freezweb/de.freezweb.heizungssteuerung/tmp/watermeter-roi-fix/alg_roi.jpg

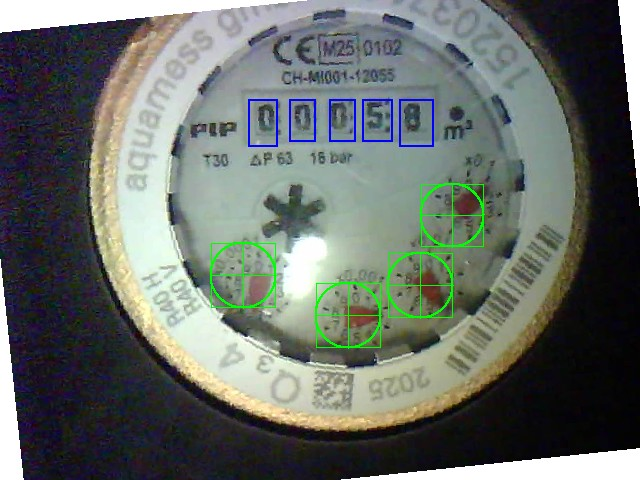
tmp/watermeter-roi-fix/alg_roi.jpg
