freezweb/de.freezweb.heizungssteuerung/tmp/watermeter-roi-fix/probe-_img_tmp_raw_jpg.jpg

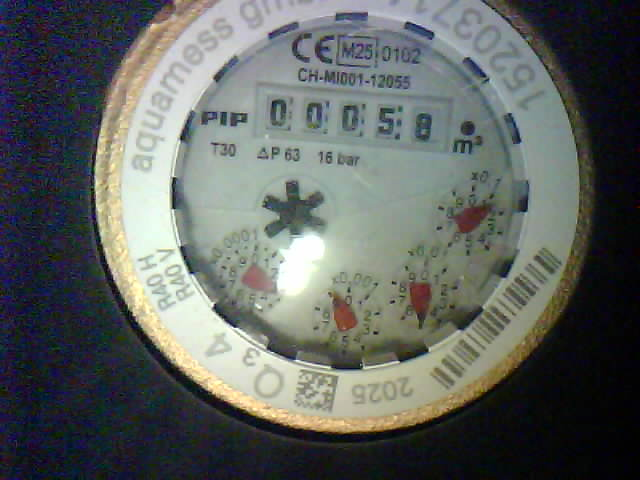
tmp/watermeter-roi-fix/probe-_img_tmp_raw_jpg.jpg
