freezweb/de.freezweb.heizungssteuerung/docs/通讯协议-0912(1)(1).docx

通讯协议Communication Protocol

Communication Protocol：9600bps，n，8,1，Communication time interval>200ms。

Support function codes :0x03,0x06，0x10
Register address | Readable | writable | Numerical range | Function Description | Remark
0(0x0000) | 0x03 | 0x06 0x10 | 0-1 | 0Power off 1Power on
1(0x0001) | 0x03 | 0x06 0x10 | 0-3 | 0 Automatic 1 Cooling 2 Heating 3 Ventilation
2(0x0002) | 0x03 | 0x06 0x10 | 0-4 | Set wind speed: 0 Auto wind 1 Low wind 2 Medium wind 3 High wind 4 Strong wind
3(0x0003) | 0x03 | 0x06 0x10 | 8-39 | Set temperature | Between the upper and lower limits
4(0x0004) | 0x03 | 0x06 0x10 | 0-1 | 0Up and down swing wind stop 1Up and down swing
5(0x0005) | 0x03 | 0x06 0x10 | 0-1 | 0Sway left and right, wind stops 1Swaying left and right
6(0x0006) | 0x03 | 0x06 0x10 | 0-1 | 0Electric heating off 1Electric heating is allowed to be turned on.
7(0x0007) | 0x03 | 0x06 0x10 | 0-1 | 0Screen display on 1Screen off
8(0x0008) | 0x03 | 0x06 0x10 | 0-1 | 0Child lock unlocking 1Child lock
9(0x0009) | 0x03 | 0x06 0x10 | 0-1 | 0Antifreeze function off 1Turn on antifreeze function
10(0x000A) | 0x03 | 0x06 0x10 | 20-39 | Anti-cold air setting temperature
11(0x000B) | 0x03 | 0x06 0x10 | 0-2 | 0Turn off the fan when the set temperature is reached. 1When the temperature reaches the set point, the fan does not turn off; when the temperature rises, the fan turns off. 2The fan does not turn off when cooling or heating reaches the set temperature.
12(0x000C) | 0x03 | 0x06 0x10 | 1-3 | Temperature control hysteresis
13(0x000D) | 0x03 | 0x06 0x10 | 0-1 | 0No power loss memory 1Has power failure memory
14(0x000E) | 0x03 | 0x06 0x10 | 1-99 | RS485 Address
20(0x0014) | 0x03 | | 0-84 | Ambient temperature | Actual temperature=n-9 0=-9 1=-8… 9=0 10=1 … 84=75
21(0x0015) | 0x03 | | 0-84 | Coil temperature | Actual temperature=N-9 0=-9 1=-8… 9=0 10=1 … 84=75
22(0x0016) | 0x03 | | 0-200 | Current real-time speed | rotational speed N*10 0Stop the wind 1-9Wind speed settings 1low wind 2medium-speed wind 3High-speed wind 4strong winds 10~200Wind speed value rotational speed N*10
23(0x0017) | 0x03 | | 0-65535 | Bit0:Ambient temperature sensor malfunction Bit1：Pipeline temperature sensor malfunction Bit2：Valve output markings Bit3：Passive point closure marker Bit4：Antifreeze in progress Bit5：Cold air protection in progress Bit6：Fan failure
