freezweb/de.freezweb.heizungssteuerung/hardware/pumpengruppe-rs485/tmp-ai-edge/live-2026-07-10-modeltest/downloads/log_data_data_1970-01-01.csv

1970-01-01T01:00:38+0100 | zaehlerstand | 33332.6666 | 58.01970 | 0.0000 | Rate too high - Read: 33332.6666 - Pre: 58.0197 - Rate: 33274.6469 | 2.8 | 2.8 | 2.8 | 2.8 | 2.8 | 7.0 | 7.0 | 7.0 | 7.0
1970-01-01T01:00:38+0100 | zaehlerstand | 11111.6666 | 58.01970 | 0.0000 | Rate too high - Read: 11111.6666 - Pre: 58.0197 - Rate: 11053.6469 | 1.0 | 1.0 | 1.0 | 1.0 | 1.0 | 7.0 | 7.0 | 7.0 | 7.0
