freezweb/de.freezweb.heizungssteuerung/hardware/pumpengruppe-rs485/tmp-ai-edge/live-2026-07-10-modeltest/downloads/log_data_data_2026-07-10.csv

2026-07-10T13:09:13+0200 | zaehlerstand | 33332.6666 | 33332.6666 | 33332.6666 | 0.0000 | no error | 2.8 | 2.8 | 2.8 | 2.8 | 2.8 | 7.0 | 7.0 | 7.0 | 7.0
2026-07-10T14:01:27+0200 | zaehlerstand | 00058.0197 | 58.0197 | 58.0197 | -33274.6469 | no error | 9.8 | 10.0 | 10.0 | 5.0 | 8.0 | 0.2 | 1.4 | 0.0 | 7.3
2026-07-10T14:17:40+0200 | zaehlerstand | 33332.6666 |  | 58.01970 | 0.0000 | Rate too high - Read: 33332.6666 - Pre: 58.0197 - Rate: 33274.6469 | 2.8 | 2.8 | 2.8 | 2.8 | 2.8 | 7.0 | 7.0 | 7.0 | 7.0
2026-07-10T14:40:03+0200 | zaehlerstand | 33332.6666 |  | 58.01970 | 0.0000 | Rate too high - Read: 33332.6666 - Pre: 58.0197 - Rate: 33274.6469 | 2.8 | 2.8 | 2.8 | 2.8 | 2.8 | 7.0 | 7.0 | 7.0 | 7.0
2026-07-10T14:45:20+0200 | zaehlerstand | 33332.6666 |  | 58.01970 | 0.0000 | Rate too high - Read: 33332.6666 - Pre: 58.0197 - Rate: 33274.6469 | 2.8 | 2.8 | 2.8 | 2.8 | 2.8 | 7.0 | 7.0 | 7.0 | 7.0
2026-07-10T15:41:46+0200 | zaehlerstand | 23344.4658 |  | 58.01970 | 0.0000 | Rate too high - Read: 23344.4658 - Pre: 58.0197 - Rate: 23286.4461 | 2.6 | 3.4 | 2.8 | 4.6 | 4.5 | 4.5 | 7.0 | 6.1 | 8.2
