freezweb/de.freezweb.heizungssteuerung/hardware/pumpengruppe-rs485/tmp-ai-edge/capture.jpg

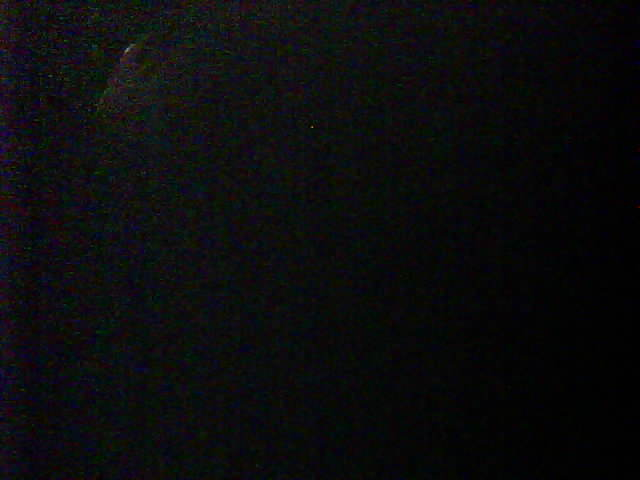
hardware/pumpengruppe-rs485/tmp-ai-edge/capture.jpg
