freezweb/de.freezweb.heizungssteuerung/hardware/pumpengruppe-rs485/tmp-ai-edge/live-2026-07-10-1545/reference.jpg

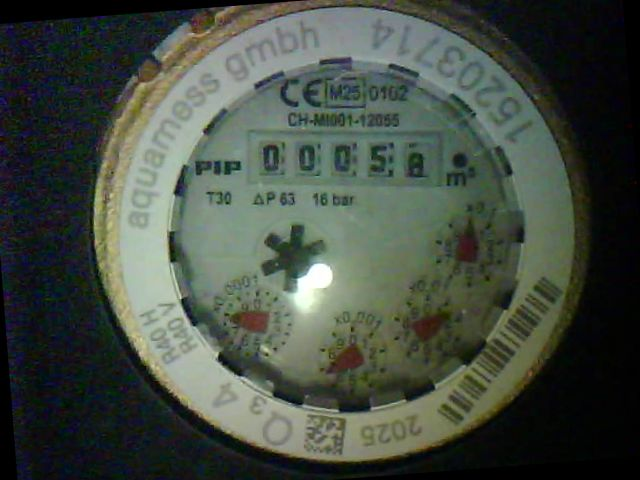
hardware/pumpengruppe-rs485/tmp-ai-edge/live-2026-07-10-1545/reference.jpg
