freezweb/de.freezweb.heizungssteuerung/hydraulik_waermepumpe_komponentenliste.xlsx

Sheet: Gesamtkonzept
Hydraulisches Gesamtkonzept Wärmepumpe / Heizung / Pool / Brunnenkühlung
Stand | 2026-06-25
Grundannahmen | 2× Monoblock-Wärmepumpe außen; je WP eigene Pumpe und motorisches Ventil/3WV, alternierend oder parallel fahrbar.
 | WP-Sammelschiene bei den Wärmepumpen; Sammelleitung über Dach/First in Heizungsraum; am First je VL/RL Entlüfter mit Absperrkugelhahn.
 | Heizungsraum wird komplett neu aufgebaut; vorhandenes Ausdehnungsgefäß bleibt. Dort sitzen Ölbrenner-Einbindung, Abgänge Pool und Nebengebäude sowie Weiterleitung ins Haupthaus.
 | Haupthausleitung bleibt bestehen; im Haupthaus bleiben die 2 bestehenden Heizkreise FBH und Radiatoren mit vorhandenen 3WV/Pumpen; Kaltwassergeräte/Fan-Coils bekommen neuen Kreis/HKV.
 | Brunnenpumpe bleibt; neu benötigt werden Brunnen-Wärmetauscher, Ventil(e), Gebäudekühlkreis-Armaturen und Mess-/Sicherheitskomponenten.
 | Pool bekommt Wärmetauscher und eigene Dosierstrecke mit pH, Redox/Chlor, pH-, Chlor und Flockungsmittel per Einzel-Schlauchpumpen; Steuerung erfolgt durch eigene Steuerung.
Schema WP-Seite | WP1 → Absperrung/Flex/Filter/Pumpe/Rückschlag/motorisches Ventil → WP-Sammelschiene
 | WP2 → Absperrung/Flex/Filter/Pumpe/Rückschlag/motorisches Ventil → WP-Sammelschiene
 | WP-Sammelschiene VL/RL → Sammelleitung über Dach/First → Heizungsraum
Schema Heizungsraum | Sammelleitung von WP-Seite → Haupt-Sammelpunkt warm VL/RL → Ölbrenner, Pool-WT, Nebengebäude, Haupthaus
Schema Haupthaus | Leitung aus Heizungsraum → Haupthaus-Verteiler → FBH-EG (bestehend), Radiatoren (bestehend), Kaltwassergeräte/Fan-Coils (neu)
Schema Brunnenkühlung | Brunnen offen: Brunnen → Brunnenpumpe → Filter/Ventil → Brunnen-WT → Ablauf/Schluckbrunnen
 | Gebäude geschlossen: Brunnen-WT → Kalt-VL → Fan-Coil-HKV → Kalt-RL → Brunnen-WT
Schema Pool | Heizungsseite: Hauptsammler → 3WV/Zonenventil → Pool-Heizkreispumpe → Pool-Plattenwärmetauscher → Rücklauf
 | Poolseite: Pool → Filterpumpe/Filter → Messstrecke/Dosierstellen → Pool-WT → zurück Pool
Betriebslogik WP | Nur WP1: Pumpe WP1 an, Ventil WP1 offen; WP2 aus und Ventil zu.
 | Nur WP2: Pumpe WP2 an, Ventil WP2 offen; WP1 aus und Ventil zu.
 | Parallel: beide Pumpen an, beide Ventile offen. Rückschlagventile verhindern Fehlzirkulation.
 | Abtauung/Störung: betroffene WP hydraulisch sperren, andere WP kann weiterlaufen.
Wichtige Hinweise | Komponentenliste ist eine Planungs-/Einkaufsliste, keine Ausführungsplanung nach DIN. Sicherheitsrelevante Auslegung, Druckverlust, MAG-Größe, Frostschutz und elektrische Verdrahtung vor Bau prüfen.
 | Günstige Links sind Einkaufs-/Suchlinks. Vor Bestellung: Anschlussmaß, Temperatur, Druck, Medium, Zulassung und Sauerstoffdichtheit prüfen.

Sheet: Komponentenliste
ID | Baugruppe | Einbauort / genaue Position | Komponente | Neu/Bestand | Menge | Dimension / Spezifikation | Funktion / Beschreibung | Günstiger Einkaufslink / Suchlink | Preis grob € | Gesamt grob € | Priorität | Hinweise / Prüfen
WP-001 | WP-Seite außen | WP1 direkt am 1" Außengewinde VL/RL | Kurzer flexibler Heizungsanschluss | Neu | 2 | 1" IG/AG, Edelstahlwellrohr/Panzerschlauch, 30–50 cm | Schwingungsentkopplung direkt an WP1, nicht als lange Leitung verwenden | https://www.amazon.de/s?k=edelstahlwellrohr+1+zoll+flexibel+heizung | 25 | 50 | hoch | Temperatur/Druck und Sauerstoffthema egal, da Metall; möglichst kurz halten
WP-002 | WP-Seite außen | WP2 direkt am 1" Außengewinde VL/RL | Kurzer flexibler Heizungsanschluss | Neu | 2 | 1" IG/AG, Edelstahlwellrohr/Panzerschlauch, 30–50 cm | Schwingungsentkopplung direkt an WP2 | https://www.amazon.de/s?k=edelstahlwellrohr+1+zoll+flexibel+heizung | 25 | 50 | hoch | Möglichst kurze flexible Strecke
WP-003 | WP-Seite außen | Je WP vor und nach Filter/Pumpe | Kugelhahn / Absperrhahn | Neu | 8 | 1" IG, voller Durchgang | Absperren von WP1/WP2 VL/RL für Wartung | https://www.amazon.de/s?k=kugelhahn+1+zoll+heizung | 12 | 96 | hoch | Messing/Heizung geeignet; full bore bevorzugt
WP-004 | WP-Seite außen | WP1 Rücklauf vor Wärmepumpe | Schmutzfänger Y-Filter | Neu | 1 | 1" IG, Heizung | Schützt WP1-Wärmetauscher/Pumpe vor Schmutz | https://www.amazon.de/s?k=schmutzf%C3%A4nger+1+zoll+heizung | 18 | 18 | hoch | Maschenweite nicht zu fein, Spülbarkeit sinnvoll
WP-005 | WP-Seite außen | WP2 Rücklauf vor Wärmepumpe | Schmutzfänger Y-Filter | Neu | 1 | 1" IG, Heizung | Schützt WP2-Wärmetauscher/Pumpe vor Schmutz | https://www.amazon.de/s?k=schmutzf%C3%A4nger+1+zoll+heizung | 18 | 18 | hoch | Herstellerforderung der WP prüfen
WP-006 | WP-Seite außen | WP1 Vorlauf/Rücklauf-Einbindung vor WP-Sammelschiene | WP1-Umwälzpumpe | Neu | 1 | mind. 25-80/180, besser nach Druckverlustrechnung; ca. 3,1 m³/h | Eigenständige Förderpumpe für WP1, weil WP laut Lastenheft keine integrierte Pumpe hat | https://chm-pumpen.de/Heizungspumpe-Auto-25-80-180/248 | 91 | 91 | hoch | Billigpumpe als Sparvariante; Premiumvergleich Grundfos 32-80 separat prüfen
WP-007 | WP-Seite außen | WP2 Vorlauf/Rücklauf-Einbindung vor WP-Sammelschiene | WP2-Umwälzpumpe | Neu | 1 | mind. 25-80/180, besser nach Druckverlustrechnung; ca. 3,1 m³/h | Eigenständige Förderpumpe für WP2 | https://chm-pumpen.de/Heizungspumpe-Auto-25-80-180/248 | 91 | 91 | hoch | Wenn 63er langer Strang und viele Bögen: ggf. 32-80 wählen
WP-008 | WP-Seite außen | Direkt hinter WP1-Pumpe Richtung Sammelschiene | Rückschlagventil | Neu | 1 | 1" oder passend zur Pumpenverschraubung | Verhindert Rückströmung durch stehende WP1 | https://www.amazon.de/s?k=r%C3%BCckschlagventil+1+zoll+heizung | 15 | 15 | hoch | Strömungsrichtung eindeutig markieren
WP-009 | WP-Seite außen | Direkt hinter WP2-Pumpe Richtung Sammelschiene | Rückschlagventil | Neu | 1 | 1" oder passend zur Pumpenverschraubung | Verhindert Rückströmung durch stehende WP2 | https://www.amazon.de/s?k=r%C3%BCckschlagventil+1+zoll+heizung | 15 | 15 | hoch | Federbelastet mit geringem Öffnungsdruck bevorzugt
WP-010 | WP-Seite außen | WP1 zwischen Pumpe/Rückschlag und WP-Sammelschiene | Motorisches Zonenventil oder 3WV WP1 | Neu | 1 | 1" bis 1¼", 230 V oder 24 V, Auf/Zu | WP1 hydraulisch in Sammelkreis ein-/auskoppeln für Alternation/Parallelbetrieb | https://www.idealo.de/preisvergleich/Liste/116030402/2-wege-motorkugelhahn-230v.html | 38 | 38 | hoch | 2WV reicht meist; echtes 3WV nur nötig, wenn Bypass/Umlenkung geplant
WP-011 | WP-Seite außen | WP2 zwischen Pumpe/Rückschlag und WP-Sammelschiene | Motorisches Zonenventil oder 3WV WP2 | Neu | 1 | 1" bis 1¼", 230 V oder 24 V, Auf/Zu | WP2 hydraulisch in Sammelkreis ein-/auskoppeln | https://www.idealo.de/preisvergleich/Liste/116030402/2-wege-motorkugelhahn-230v.html | 38 | 38 | hoch | Stellzeit/Fail-Position beachten
WP-012 | WP-Seite außen | WP1/WP2 bis WP-Sammelschiene | PP-RCT Heizungsrohr | Neu | 20 | 50 mm, sauerstoffdicht DIN 4726, Stabi/Alu/Faser | Kurze großdimensionierte Anbindung beider Wärmepumpen an WP-Sammelschiene | https://www.kwerk.de/rohrsysteme/pp-rct-rohrsysteme/pp-rct-rohre/rohre-mehrlagig/stabitec-ct/pp-rct-alu-druckrohr-stabitec-ct-20mpa-gruen/ | 8 | 160 | hoch | Nur heizungsgeeignet und sauerstoffdicht; Menge Meter grob
WP-013 | WP-Seite außen | Sammelleitung WP-Sammelschiene → Heizungsraum über First | PP-RCT Heizungsrohr Sparvariante | Neu | 50 | 63 mm, sauerstoffdicht DIN 4726, Stabi/Alu/Faser | Gemeinsamer VL/RL über Dach/First in Heizungsraum | https://www.kwerk.de/rohrsysteme/pp-rct-rohrsysteme/pp-rct-rohre/rohre-mehrlagig/stabitec-ct/pp-rct-alu-druckrohr-stabitec-ct-20mpa-gruen/ | 12 | 600 | hoch | 63 mm ist Material-/Werkzeug-Sparvariante; 75 mm hydraulisch besser
WP-014 | WP-Seite außen | Alternative zur 63er Sammelleitung | PP-RCT Heizungsrohr Komfortvariante | Optional | 50 | 75 mm, sauerstoffdicht DIN 4726 | Hydraulisch bessere gemeinsame Sammelleitung | https://www.rohrleitungssysteme.de/pp-r-rohrsysteme/index.php?zurueck=1 | 18 | 900 | mittel | Nur wenn Werkzeug/Fittings bezahlbar verfügbar
WP-015 | Werkzeug | Für PP-RCT 40/50/63 mm | Muffenschweißgerät | Neu | 1 | bis 63 mm, passende Muffen | Werkzeug zum Verarbeiten von PP-R/PP-RCT | https://www.amazon.de/s?k=muffenschwei%C3%9Fger%C3%A4t+63mm+ppr | 60 | 60 | hoch | Bei Alu-Stabi zusätzlich Schälgerät nötig; Probeschweißungen machen
WP-016 | Werkzeug | Für PP-RCT Alu-Stabi Rohr | Schälgerät / Rohrschäler | Neu | 1 | 40/50/63 mm passend zum Rohrsystem | Entfernt Aluschicht vor Schweißung bei Stabi-Rohr | https://www.rohrleitungssysteme.de/pp-r-rohrsysteme/index.php?zurueck=1 | 80 | 80 | hoch | Systemgebunden; beim Rohrhändler passend mitbestellen
WP-017 | WP-Sammelschiene außen | An Sammel-VL und Sammel-RL | Temperaturfühler Anlegefühler | Neu | 2 | PT1000, Anlegefühler | Messung WP-Sammel-VL/RL für Steuerung | https://www.amazon.de/s?k=pt1000+anlegef%C3%BChler+heizung | 15 | 30 | hoch | An Rohr gut wärmeleitend befestigen und dämmen
WP-018 | WP-Sammelschiene außen | Tiefpunkt WP-Sammelschiene VL/RL | KFE-Hahn / Entleerung | Neu | 2 | 1/2" oder 3/4" | Entleeren/Spülen der WP-Seite | https://www.amazon.de/s?k=kfe+hahn+1%2F2+heizung | 8 | 16 | mittel | Mit Schlauchanschluss
WP-019 | Dach/First | Höchster Punkt der Sammelleitung, Vorlauf | T-Stück + Kugelhahn + automatischer Entlüfter | Neu | 1 | passend 63 mm → 1/2" Entlüfter | Entlüftet Vorlauf am First; Kugelhahn ermöglicht Austausch | https://www.amazon.de/s?k=automatischer+entl%C3%BCfter+1%2F2+heizung | 18 | 18 | hoch | Nicht ohne Absperrhahn montieren
WP-020 | Dach/First | Höchster Punkt der Sammelleitung, Rücklauf | T-Stück + Kugelhahn + automatischer Entlüfter | Neu | 1 | passend 63 mm → 1/2" Entlüfter | Entlüftet Rücklauf am First | https://www.amazon.de/s?k=automatischer+entl%C3%BCfter+1%2F2+heizung | 18 | 18 | hoch | Zusätzlich manuelle Entlüftung sinnvoll
WP-021 | Dach/First | Komplette Leitung im Dach/Spitz | Rohrisolierung | Neu | 50 | für 63 mm Rohr, dick, wärme-/frostgeeignet | Reduziert Verluste im Spitz und schützt gegen Kondensat/Frost | https://www.amazon.de/s?k=rohrisolierung+63mm+heizung | 10 | 500 | hoch | Preis pro Meter stark abhängig von Dämmstärke; Außen-/Kaltbereich beachten
HR-001 | Heizungsraum Hauptsammler | Eintritt Sammelleitung von WP-Seite | Haupt-VL/RL-Sammler / Verteiler | Neu | 1 | mind. DN50/63, 4 Abgänge: Ölbrenner, Pool, Nebengebäude, Haupthaus | Zentraler warmer Sammelpunkt im Heizungsraum | https://www.amazon.de/s?k=heizungsverteiler+sammelschiene+3+abg%C3%A4nge | 180 | 180 | hoch | Kann aus PP-RCT-Teilen gebaut werden; alle Abgänge absperrbar
HR-002 | Heizungsraum Hauptsammler | Haupt-Rücklauf vor WP-Sammelleitung | Magnetit-/Schlammabscheider | Neu | 1 | 1¼" bis 2", passend zum Hauptvolumenstrom | Schützt WP, Pumpen und Wärmetauscher vor Magnetit/Schlamm | https://www.amazon.de/s?k=magnetitabscheider+1+zoll+heizung | 80 | 80 | hoch | Nicht zu klein wählen; Spülmöglichkeit nach unten
HR-003 | Heizungsraum Hauptsammler | Hauptsammler oben | Automatischer Entlüfter mit Absperrung | Neu | 1 | 1/2" | Entlüftung am höchsten Punkt im Heizungsraum | https://www.amazon.de/s?k=automatischer+entl%C3%BCfter+1%2F2+heizung | 15 | 15 | mittel | Bei Dach-First-Entlüftern trotzdem sinnvoll
HR-004 | Heizungsraum Hauptsammler | Hauptsammler / Sicherheitsgruppe | Sicherheitsgruppe Heizung | Neu | 1 | 3 bar, Manometer, Sicherheitsventil | Sicherheitsausrüstung des Heizkreises | https://www.amazon.de/s?k=sicherheitsgruppe+heizung+3+bar | 35 | 35 | hoch | Bestehendes MAG bleibt, Größe/Einstellung prüfen
HR-005 | Heizungsraum Hauptsammler | Rücklauf / Füllpunkt | Füll-/Spülarmatur | Neu | 1 | KFE / Systemtrenner nach Bedarf | Befüllen, Spülen, Nachfüllen der Heizungsanlage | https://www.amazon.de/s?k=heizung+f%C3%BCll+sp%C3%BCl+armatur | 35 | 35 | mittel | Trinkwasser-Nachspeisung fachgerecht mit Systemtrenner
HR-006 | Heizungsraum Hauptsammler | Tiefpunkt Hauptsammler | KFE-Hahn / Entleerung | Neu | 2 | 1/2" oder 3/4" | Entleerung VL/RL Heizungsraum | https://www.amazon.de/s?k=kfe+hahn+1%2F2+heizung | 8 | 16 | mittel | Je tiefem Punkt
HR-007 | Heizungsraum Hauptsammler | Gesamt-VL/RL Heizungsraum | Temperaturfühler | Neu | 2 | PT1000 Anlegefühler | Messung Gesamt-VL/RL für Steuerung | https://www.amazon.de/s?k=pt1000+anlegef%C3%BChler+heizung | 15 | 30 | hoch | Fühler gut dämmen
HR-008 | Heizungsraum Ölbrenner | Abgang Ölbrenner vom Hauptsammler | Ölbrenner-Einbindung mit Absperrungen/RV | Neu/Prüfen | 1 | Kugelhähne + Rückschlag + vorhandene Kesselpumpe prüfen | Übergangsquelle im Heizungsraum | https://www.amazon.de/s?k=kugelhahn+1+zoll+heizung | 60 | 60 | mittel | Ölbrenner selbst bleibt; Pumpenzustand prüfen
HR-009 | Heizungsraum Haupthausabgang | Abgang Haupthaus unterhalb Hauptsammler vor Bestandsleitung | Kugelhahn VL/RL Haupthaus | Neu | 2 | passend zur Leitung, 1"/DN25 oder Übergang | Haupthausleitung absperrbar machen | https://www.amazon.de/s?k=kugelhahn+1+zoll+heizung | 12 | 24 | hoch | Direkt am Sammler
HR-010 | Heizungsraum Haupthausabgang | Abgang Haupthaus vor vorhandener Leitung | Haupthaus-Strangpumpe | Prüfen/Optional | 1 | 25-60/180 oder 25-80/180 je nach Bestandsleitung | Fördert nur Haupthaus, falls vorhandene Pumpen nicht ausreichend ziehen | https://chm-pumpen.de/Heizungspumpe-Auto-25-80-180/248 | 91 | 91 | mittel | Wenn FBH/Radiatorpumpen schon saugen, ggf. nicht nötig
HR-011 | Heizungsraum Haupthausabgang | Haupthaus-VL/RL vor Bestandsleitung | Temperaturfühler Haupthaus VL/RL | Neu | 2 | PT1000 | Leistungs-/Spreizungsüberwachung Haupthaus | https://www.amazon.de/s?k=pt1000+anlegef%C3%BChler+heizung | 15 | 30 | hoch | Hilft zu prüfen, ob alte Leitung reicht
HR-012 | Heizungsraum Haupthausabgang | Optional in Haupthausstrang | Wärmemengenzähler / Durchflussmesser | Optional | 1 | DN25/1", M-Bus/Impuls/Modbus | Reale kW ins Haupthaus messen | https://www.amazon.de/s?k=w%C3%A4rmemengenz%C3%A4hler+DN25+M-Bus | 90 | 90 | niedrig | Sehr hilfreich für Inbetriebnahme, aber nicht zwingend
POOL-H-001 | Pool Heizungsseite | Heizungsraum, Abgang Pool vom Hauptsammler | Motorisches 3WV/Zonenventil Pool | Neu | 1 | 1"–1¼", 230V/24V | Pool-Heizkreis freigeben/umschalten | https://www.amazon.de/wege-motorkugelhahn-230v-elektrisch-kugelventil/dp/B07GCGFQ47 | 42 | 42 | hoch | Bei nur Ein/Aus reicht 2WV; 3WV für Bypass/Regelung
POOL-H-002 | Pool Heizungsseite | Nach Pool-Ventil vor Pool-WT | Pumpe Pool-Heizkreis | Neu | 1 | 25-60/180 oder 25-80/180 | Fördert Heizungswasser durch Pool-WT | https://chm-pumpen.de/Heizungspumpe-Auto-25-80-180/248 | 91 | 91 | hoch | Volumenstrom nach WT-Datenblatt wählen
POOL-H-003 | Pool Heizungsseite | Heizungsraum, zwischen Heizungsseite und Poolseite | Pool-Plattenwärmetauscher | Neu | 1 | mind. 50 kW Edelstahl; bei Chlorid/Salz ggf. Titan prüfen | Trennt Heizungswasser vom Poolwasser | https://www.schwimmbadbau24.de/Plattenwaermetauscher-PWT-50-kW-Edelstahl-geloetet | 180 | 180 | hoch | Für Chlor/Salz auf Materialfreigabe achten
POOL-H-004 | Pool Heizungsseite | Vor und nach Pool-WT Heizungsseite | Kugelhähne + Verschraubungen | Neu | 4 | 1" oder passend zum WT | WT absperren und wartbar machen | https://www.amazon.de/s?k=kugelhahn+1+zoll+heizung | 12 | 48 | mittel | Mit lösbarer Verschraubung
POOL-H-005 | Pool Heizungsseite | Pool-WT Heizungs-VL/RL | Temperaturfühler Pool-WT Heizungsseite | Neu | 2 | PT1000 | Regelung und Kontrolle der Heizleistung | https://www.amazon.de/s?k=pt1000+anlegef%C3%BChler+heizung | 15 | 30 | mittel | Auf Metallfitting/Anlegepunkt
POOL-H-006 | Pool Heizungsseite | Rücklauf Pool-Heizkreis | Rückschlagventil Pool | Neu | 1 | 1" | Verhindert Fehlzirkulation | https://www.amazon.de/s?k=r%C3%BCckschlagventil+1+zoll+heizung | 15 | 15 | mittel | Strömungsrichtung markieren
POOL-W-001 | Poolwasserseite | Pooltechnik vor Pool-WT | Poolwasserseitige Bypass-Verrohrung | Neu | 1 | PVC-U 50/63, Kugelhähne, Bypass | Pool-WT in Filterkreis einbinden | https://www.amazon.de/s?k=pool+filterpumpe+inverter | 80 | 80 | hoch | Bestands-Filteranlage berücksichtigen
POOL-W-002 | Poolwasserseite | Pooltechnik vor Dosier-/WT-Strecke | Durchflussschalter Pool | Neu | 1 | PVC 50/63, Reed/Schalter | Dosierung nur bei Durchfluss erlauben | https://www.amazon.de/s?k=durchflussschalter+pool+50mm | 25 | 25 | hoch | Sicherheitsfreigabe für Dosierpumpen
POOL-W-003 | Poolwasserseite | Pooltechnik Rücklauf nach Filter, vor Dosierung | Pool-Temperaturfühler | Neu | 1 | PT1000 oder DS18B20 in Tauchhülse | Pooltemperatur für Heizlogik | https://www.amazon.de/s?k=pt1000+anlegef%C3%BChler+heizung | 15 | 15 | hoch | Tauchhülse in PVC bevorzugt
NG-001 | Nebengebäude | Heizungsraum, Abgang Nebengebäude vom Hauptsammler | Motorisches 3WV/Zonenventil Nebengebäude | Neu | 1 | 1"–1¼", 230V/24V | Nebengebäude freigeben/umschalten | https://www.amazon.de/wege-motorkugelhahn-230v-elektrisch-kugelventil/dp/B07GCGFQ47 | 42 | 42 | hoch | Wenn nur Ein/Aus, 2WV reicht
NG-002 | Nebengebäude | Nach Ventil im Nebengebäude-Abgang | Pumpe Nebengebäude | Neu | 1 | 25-60/180 oder 25-80/180 | Fördert Nebengebäude-Kreis | https://chm-pumpen.de/Heizungspumpe-Auto-25-80-180/248 | 91 | 91 | hoch | Für ca. 10 kW Heizlast, Leitungslänge prüfen
NG-003 | Nebengebäude | Abgang Nebengebäude VL/RL im Heizungsraum | Kugelhähne VL/RL | Neu | 2 | 1"–1¼" | Nebengebäude absperrbar | https://www.amazon.de/s?k=kugelhahn+1+zoll+heizung | 12 | 24 | hoch | Direkt am Sammler
NG-004 | Nebengebäude | Nebengebäude VL/RL | Temperaturfühler | Neu | 2 | PT1000 | Regelung/Überwachung Nebengebäude | https://www.amazon.de/s?k=pt1000+anlegef%C3%BChler+heizung | 15 | 30 | mittel | Einbauort Heizungsraum oder Nebengebäude
NG-005 | Nebengebäude | Rücklauf Nebengebäude | Rückschlagventil | Neu | 1 | 1" | Verhindert Schwerkraft-/Fehlzirkulation | https://www.amazon.de/s?k=r%C3%BCckschlagventil+1+zoll+heizung | 15 | 15 | mittel | Nach Pumpe oder im Rücklauf
HH-001 | Haupthaus Keller | Keller-Sammelschiene für 3 Abgänge | Haupthaus-Verteiler/Sammelschiene 3 Abgänge | Neu | 1 | 3 Abgänge: FBH, Radiatoren, Kaltwassergeräte; passend zu Bestandsleitung | Ersetzt alte Sammelschiene mit nur 2 Abgängen | https://www.amazon.de/s?k=heizkreisverteiler+3+abg%C3%A4nge+DN25 | 160 | 160 | hoch | So bauen, dass bestehende FBH/Radiatoren weiterverwendet werden
HH-002 | Haupthaus FBH | Bestehender FBH-Abgang an neuer Sammelschiene | FBH-Mischergruppe mit Pumpe | Bestand | 1 | vorhanden | Bestehender Fußbodenheizungskreis bleibt | https://chm-pumpen.de/Heizungspumpe-Auto-25-80-180/248 | 0 |  | hoch | Nur Anschlüsse/Dichtungen/Absperrung ggf. neu
HH-003 | Haupthaus FBH | FBH-VL/RL am HKV | Temperaturfühler FBH VL/RL | Neu | 2 | PT1000 | Regelung bestehender FBH-Kreis | https://www.amazon.de/s?k=pt1000+anlegef%C3%BChler+heizung | 15 | 30 | hoch | Auch wenn Bestand: Fühler ergänzen
HH-004 | Haupthaus Radiatoren | Bestehender Radiator-Abgang an neuer Sammelschiene | Radiatoren-Mischergruppe mit Pumpe | Bestand | 1 | vorhanden | Bestehender Heizkörperkreis bleibt | https://chm-pumpen.de/Heizungspumpe-Auto-25-80-180/248 | 0 |  | hoch | Nur Anschlüsse/Dichtungen/Absperrung prüfen
HH-005 | Haupthaus Radiatoren | Radiatoren-VL/RL | Temperaturfühler Radiatoren VL/RL | Neu | 2 | PT1000 | Regelung/Überwachung Radiatoren | https://www.amazon.de/s?k=pt1000+anlegef%C3%BChler+heizung | 15 | 30 | hoch | Für Backup/hohe VL wichtig
HH-006 | Haupthaus Kaltwassergeräte | Dritter Abgang neue Keller-Sammelschiene | Kaltwassergeräte-/Fan-Coil-HKV | Neu | 1 | 5 Abgänge, mit Durchflussanzeige und Stellantrieben | Verteiler für 5 OG-Geräte: Kind, Büro, Schlafen, Bad, Flur | https://www.amazon.de/s?k=heizkreisverteiler+3+abg%C3%A4nge+DN25 | 180 | 180 | hoch | Für Heizen und Kühlen geeignete Materialien/isolierbare Ausführung
HH-007 | Haupthaus Kaltwassergeräte | Vor Fan-Coil-HKV | Pumpe Fan-Coil-Kreis | Neu | 1 | 25-60/180 oder passend zu 5 Geräten | Fördert Heiz-/Kühlwasser zu Fan-Coils | https://chm-pumpen.de/Heizungspumpe-Auto-25-80-180/248 | 91 | 91 | hoch | Bei Kühlung Kondensat beachten
HH-008 | Haupthaus Kaltwassergeräte | Zwischen Warmkreis und Kaltkreis/Fan-Coil-HKV | Umschaltventil Heizen/Kühlen | Neu | 2 | 2× 2WV oder 1× 3WV, 230V/24V | Schaltet Fan-Coil-HKV zwischen Warmwasser und Brunnenkühlung um | https://www.amazon.de/wege-motorkugelhahn-230v-elektrisch-kugelventil/dp/B07GCGFQ47 | 42 | 84 | hoch | Gegenseitige Verriegelung in Steuerung
HH-009 | Haupthaus Kaltwassergeräte | Fan-Coil-HKV Abgänge | Stellantriebe Einzelventile | Neu | 5 | 230V/24V passend zum HKV | Einzelregelung der 5 Kaltwassergeräte | https://www.amazon.de/s?k=heizkreisverteiler+3+abg%C3%A4nge+DN25 | 12 | 60 | mittel | Spannung passend zur Steuerung wählen
HH-010 | Haupthaus Kaltwassergeräte | Fan-Coil-VL/RL | Temperaturfühler Fan-Coil VL/RL | Neu | 2 | PT1000 | Regelung Fan-Coil-Kreis | https://www.amazon.de/s?k=pt1000+anlegef%C3%BChler+heizung | 15 | 30 | hoch | Auch für Taupunktlogik
HH-011 | Haupthaus Kaltwassergeräte | Fan-Coil-Kreis / Referenzräume | Taupunkt-/Feuchtefühler | Neu | 2 | Modbus/0-10V/HA-Sensor | Kühlfreigabe und Kondensationsschutz | https://www.amazon.de/s?k=ph+orp+controller+rs485+modbus+4-20ma | 40 | 80 | hoch | Link ist nur Suchlink; passenden Feuchte-/Taupunktsensor wählen
HH-012 | Haupthaus Kaltwassergeräte | Jedes Fan-Coil-Gerät | Kondensatwanne/-ablauf/-Schalter | Neu | 5 | passend zum Gerät | Sicherer Kondensatablauf bei Kühlung | https://www.amazon.de/s?k=durchflussschalter+pool+50mm | 20 | 100 | hoch | Je Gerät vorsehen
BK-001 | Brunnenkühlung offen | Brunnenleitung nach vorhandener Brunnenpumpe | Motorisches Brunnenwasser-Ventil | Neu | 1 | 1" 24V/230V, wassergeeignet | Öffnet Brunnenwasser nur bei Kühlanforderung / WT-Betrieb | https://www.idealo.de/preisvergleich/Liste/116030402/2-wege-motorkugelhahn-230v.html | 38 | 38 | hoch | Mit Brunnenpumpe/FU verriegeln
BK-002 | Brunnenkühlung offen | Vor Brunnen-WT Primärseite | Filter/Schmutzfänger Brunnenwasser | Neu | 1 | 1"–1¼", spülbar | Schützt Brunnen-Wärmetauscher vor Sand/Partikeln | https://www.amazon.de/s?k=wasserfilter+brunnenpumpe+1+zoll | 35 | 35 | hoch | Brunnenwasser kann Platten-WT schnell zusetzen
BK-003 | Brunnenkühlung offen/geschlossen | Keller, zwischen Brunnenwasser und Gebäudekühlkreis | Brunnen-Plattenwärmetauscher | Neu | 1 | Edelstahl, mind. 30–60 kW, ausreichend Volumenstrom | Trennt offenes Brunnenwasser vom geschlossenen Kaltwasserkreis | https://www.wiltec.de/wiltec-waermetauscher-50-platten-max.-285-kw-12-m3-h-2-50-l-je-durchgang-plattenwaermetauscher-aus-edelstahl-als-waermeuebertraeger/50683 | 160 | 160 | hoch | Bei eisen-/manganhaltigem Wasser größer und reinigbar planen
BK-004 | Brunnenkühlung offen | Brunnenwasser Eintritt/Austritt WT | Temperaturfühler Brunnenwasser | Neu | 2 | PT1000/Tauchfühler | Messung Kühlleistung Primärseite | https://www.amazon.de/s?k=pt1000+anlegef%C3%BChler+heizung | 15 | 30 | mittel | Tauchhülse bevorzugt
BK-005 | Brunnenkühlung offen | Brunnenleitung | Durchflussschalter / Strömungswächter | Neu | 1 | 1", Schaltausgang | Sicherstellen, dass Wasser über WT fließt | https://www.amazon.de/s?k=durchflussschalter+pool+50mm | 25 | 25 | hoch | Schützt vor Trocken-/Fehlbetrieb
BK-006 | Brunnenkühlung geschlossen | Gebäudeseite Brunnen-WT | Kleines Ausdehnungsgefäß Kaltwasserkreis | Neu | 1 | 8–18 l, je Wasserinhalt | Druckhaltung geschlossener Kaltwasserkreis | https://www.amazon.de/s?k=ausdehnungsgef%C3%A4%C3%9F+heizung | 35 | 35 | mittel | Wenn Kaltwasserkreis hydraulisch separater Kreis ist
BK-007 | Brunnenkühlung geschlossen | Gebäudeseite Brunnen-WT | Sicherheitsgruppe / Manometer Kaltkreis | Neu | 1 | 3 bar / passend | Sicherheit geschlossener Gebäudekühlkreis | https://www.amazon.de/s?k=sicherheitsgruppe+heizung+3+bar | 35 | 35 | mittel | Nur falls separater geschlossener Kreis
BK-008 | Brunnenkühlung geschlossen | Gebäude-Kaltkreis VL/RL | Temperaturfühler Kalt-VL/Kalt-RL | Neu | 2 | PT1000 | Regelung Brunnenkühlung und Taupunktgrenze | https://www.amazon.de/s?k=pt1000+anlegef%C3%BChler+heizung | 15 | 30 | hoch | Direkt nach WT und Rücklauf vor WT
BK-009 | Brunnenkühlung geschlossen | Kaltkreis an Hochpunkt/HKV | Entlüfter + Absperrung | Neu | 1 | 1/2" | Entlüftung Kaltwasserkreis | https://www.amazon.de/s?k=automatischer+entl%C3%BCfter+1%2F2+heizung | 15 | 15 | mittel | Bei Kühlung gut dämmen gegen Kondensat
BK-010 | Brunnenkühlung geschlossen | Kaltkreis Tiefpunkt | Entleer-/Spülhähne | Neu | 2 | KFE | Spülen/Befüllen Kaltwasserkreis | https://www.amazon.de/s?k=kfe+hahn+1%2F2+heizung | 8 | 16 | mittel | Mit Schlauchanschluss
DOS-001 | Pool Dosierung Messung | Pooltechnik, Bypass nach Filter vor Dosierstellen | Acryl-Messzelle / Messrohr 2-fach | Neu | 1 | pH + Redox, 12 mm/PG13.5, Durchflussarmatur | Ruhige Messstrecke für pH und Redox/ORP | https://www.gemke-shop.de/dosiertechnik/schwimmbad/elektroden/ | 190 | 190 | hoch | Gemke/Pooldigital; Bypass mit Probeentnahme bevorzugt
DOS-002 | Pool Dosierung Messung | In Messzelle Steckplatz pH | pH-Elektrode BNC | Neu | 1 | Pool geeignet, BNC, 12 mm/PG13.5 passend zur Messzelle | Misst pH-Wert | https://www.idealo.de/preisvergleich/Liste/123483211/ph-elektrode-bnc-pool.html | 70 | 70 | hoch | Billige Sonden möglich, aber regelmäßig kalibrieren/ersetzen
DOS-003 | Pool Dosierung Messung | In Messzelle Steckplatz Redox | Redox-/ORP-Elektrode BNC | Neu | 1 | Pool geeignet, BNC, passend zur Messzelle | Indirekte Chlorregelung über Redox | https://www.idealo.de/preisvergleich/Liste/123492102/redox-elektrode-pool.html | 98 | 98 | hoch | Freies Chlor separat per DPD prüfen/kalibrieren
DOS-004 | Pool Dosierung Elektronik | Schaltschrank Poolsteuerung | pH-Messumformer | Neu | 1 | BNC → 0-10V/4-20mA/RS485-Modbus | Wandelt pH-Elektrodensignal für eigene Steuerung | https://www.antratek.de/industrial-ph-meter-sensor-modbus-rtu-rs485 | 165 | 165 | hoch | BNC direkt an RevPi-AI geht nicht sinnvoll ohne Messumformer
DOS-005 | Pool Dosierung Elektronik | Schaltschrank Poolsteuerung | Redox-/ORP-Messumformer | Neu | 1 | BNC → 0-10V/4-20mA/RS485-Modbus | Wandelt Redox-Signal für eigene Steuerung | https://www.amazon.de/s?k=ph+orp+controller+rs485+modbus+4-20ma | 120 | 120 | hoch | Modbus/4-20mA bevorzugt
DOS-006 | Pool Dosierung pH- | Chemikalienwand, Kanister pH- → Impfventil | Schlauchpumpe pH- | Neu | 1 | 12/24V oder 230V, per Relais/PWM schaltbar, chemikaliengeeignet | Dosiert pH-Minus | https://www.amazon.de/s?k=peristaltische+dosierpumpe+12v | 25 | 25 | hoch | Schlauchmaterial säuregeeignet; Rückschlag/Impfventil
DOS-007 | Pool Dosierung Chlor | Chemikalienwand, Kanister Chlor → Impfventil | Schlauchpumpe Chlor | Neu | 1 | 12/24V oder 230V, chemikaliengeeignet | Dosiert Flüssigchlor/Natriumhypochlorit | https://www.amazon.de/s?k=peristaltische+dosierpumpe+12v | 25 | 25 | hoch | Chlorbeständige Schläuche, getrennt von Säure
DOS-008 | Pool Dosierung Flockung | Chemikalienwand, Kanister Flockung → Impfventil | Schlauchpumpe Flockungsmittel | Neu | 1 | kleine Fördermenge, chemikaliengeeignet | Dosiert Flockungsmittel | https://www.amazon.de/s?k=peristaltische+dosierpumpe+12v | 25 | 25 | mittel | Deutlich kleinere Dosiermengen nötig
DOS-009 | Pool Dosierung Einspritzung | Pool-Rücklaufleitung nach Messung/WT, pH- Stelle | Impfventil pH- | Neu | 1 | 1/2" × 4/6 mm | Einspritzpunkt pH-Minus | https://www.idealo.de/preisvergleich/Liste/122043962/impfventil-1-2.html | 18 | 18 | hoch | Nicht direkt neben Chlor-Impfstelle
DOS-010 | Pool Dosierung Einspritzung | Pool-Rücklaufleitung nach pH- mit Abstand, Chlor Stelle | Impfventil Chlor | Neu | 1 | 1/2" × 4/6 mm | Einspritzpunkt Chlor | https://www.idealo.de/preisvergleich/Liste/122043962/impfventil-1-2.html | 18 | 18 | hoch | Abstand zur Säure-Impfstelle einhalten
DOS-011 | Pool Dosierung Einspritzung | Pool-Rücklaufleitung nach Chlor mit Abstand, Flockung Stelle | Impfventil Flockungsmittel | Neu | 1 | 1/2" × 4/6 mm | Einspritzpunkt Flockung | https://www.idealo.de/preisvergleich/Liste/122043962/impfventil-1-2.html | 18 | 18 | mittel | Position nach Filterkonzept prüfen
DOS-012 | Pool Dosierung Chemie | Von Kanistern zu Pumpen/Impfventilen | Dosierschlauch | Neu | 30 | 4×6 mm PE/PTFE/PVC passend | Saug-/Druckleitungen der Dosierpumpen | https://www.amazon.de/s?k=dosierschlauch+4x6+pool | 1 | 30 | hoch | Chlor/Säure kompatibel wählen
DOS-013 | Pool Dosierung Chemie | Chemikalienwand | Sauglanzen / Fußventile | Neu | 3 | für Kanister, 4×6 mm | Saugleitung in Kanister mit Rückschlag/Filter | https://www.amazon.de/s?k=dosierschlauch+4x6+pool | 15 | 45 | hoch | Für jeden Kanister getrennt
DOS-014 | Pool Dosierung Chemie | Chemikalienlager | Chemikalienkanister / Auffangwannen | Neu | 3 | 20 l Kanister + Auffangwanne | Sichere Lagerung pH-, Chlor, Flockung | https://www.amazon.de/s?k=kanister+20l+chemikalien+dosierpumpe | 12 | 36 | hoch | Säure und Chlor räumlich getrennt lagern
DOS-015 | Pool Dosierung Wartung | Mess-/Dosieranlage | Kalibrierlösungen pH/Redox | Neu | 1 | pH 7, pH 4/10, Redox 465 mV | Kalibrierung und Kontrolle der Sonden | https://www.amazon.de/s?k=pH+Redox+Kalibrierl%C3%B6sung+Pool | 25 | 25 | hoch | Regelmäßig neu kaufen
DOS-016 | Pool Dosierung Sicherheit | Poolsteuerung, in Reihe zu Dosierfreigabe | Not-Aus / Dosierfreigabe-Relais | Neu | 1 | 24V/230V passend | Dosierpumpen nur bei Durchfluss/Filterbetrieb freigeben | https://www.amazon.de/s?k=hutschiene+koppelrelais+24v+230v | 20 | 20 | hoch | Chlor und Säure nie bei stehendem Wasser dosieren
ALL-001 | Fittings allgemein | Alle PP-RCT Übergänge Rohr ↔ Gewinde/Pumpen/Ventile | PP-RCT Fittings/Übergänge | Neu | 1 | Pauschal 40/50/63 mm, Gewinde 1"/1¼" | Muffen, T-Stücke, Reduzierungen, Übergänge zu Pumpen/Ventilen | https://www.rohrleitungssysteme.de/pp-r-rohrsysteme/index.php?zurueck=1 | 350 | 350 | hoch | Als Pauschalposition; genaue Stückliste nach Aufmaß
ALL-002 | Fittings allgemein | Alle neuen Pumpen | Pumpenverschraubungen | Neu | 5 | 1½" Pumpenseite auf 1"/1¼" Rohrseite | Anschluss der Heizungs-/Pool-/Nebengebäudepumpen | https://chm-pumpen.de/Heizungspumpe-Auto-25-80-180/248 | 12 | 60 | hoch | Oft im Lieferumfang, trotzdem einplanen
ALL-003 | Fittings allgemein | Alle neuen Rohrstrecken | Rohrschellen/Festpunkte/Gleitpunkte | Neu | 1 | für 40/50/63 mm | Befestigung und Dehnungsausgleich PP-RCT | https://www.amazon.de/s?k=rohrisolierung+63mm+heizung | 120 | 120 | hoch | PP-RCT-Längenausdehnung beachten
ALL-004 | Elektrik/Steuerung | Schaltschrank Heizungsraum/Keller | Koppelrelais für Pumpen/Ventile | Neu | 20 | 24V DC Spule → 230V Last / potentialfrei | Ausgänge RevPi auf Pumpen/Ventile/Freigaben | https://www.amazon.de/s?k=hutschiene+koppelrelais+24v+230v | 8 | 160 | hoch | Lasten sauber absichern
ALL-005 | Elektrik/Steuerung | Sensorik und Ventile | Steuerleitung / Aderleitung | Neu | 1 | LIYY/J-Y(St)Y/Ölflex je nach Strecke | Verdrahtung Fühler, Ventile, Pumpenfreigaben | https://www.amazon.de/s?k=steuerleitung+liyy+0%2C75 | 80 | 80 | mittel | Separat von 230V verlegen
ALL-006 | Dokumentation/Inbetriebnahme | Gesamtanlage | Beschriftungsmaterial / Kabelmarker / Rohrkennzeichnung | Neu | 1 | Etiketten, Schildchen, Fließrichtungspfeile | Verhindert spätere Fehlinterpretation | https://www.amazon.de/s?k=steuerleitung+liyy+0%2C75 | 30 | 30 | mittel | Jede Pumpe, jedes Ventil, jeder Sensor beschriften

Sheet: Dimensionen
Bereich | Empfehlung | Begründung / Hinweis
WP1/WP2 jeweils bis WP-Sammelschiene | 50 mm PP-RCT, sauerstoffdicht | Kurze Einzelanbindung je WP; WP-Anschluss 1" nur kurz flexibel, danach größer
WP-Sammelschiene → Heizungsraum über Dach/First | 63 mm PP-RCT als Sparvariante; 75 mm besser | Durch Firstweg ca. 25 m je Richtung; 63 mm spart Werkzeug/Material, 75 mm hydraulisch besser
Heizungsraum Hauptsammler | mind. DN50/63, mehrere Abgänge | Ölbrenner, Pool, Nebengebäude und Haupthaus separat abgreifen
Heizungsraum → Haupthaus | Bestandsleitung bleibt; bis Übergang möglichst nicht weiter verengen | Versorgt nur Haupthaus ca. 13 kW; dynamische VL/Spreizung 7–10 K
Haupthaus-Sammelschiene | 3 Abgänge | FBH Bestand, Radiatoren Bestand, Kaltwassergeräte neu
Pool-WT | mind. 50 kW, Poolmaterial prüfen | Pool 35 °C ganzjährig; Chlorid/Salz kann Edelstahl begrenzen, ggf. Titan
Brunnen-WT | 30–60 kW oder größer, reinigbar/absperrbar | Freie Kühlung; Brunnenwasser kann verschmutzen, Filter vor WT
Dosierung | Messzelle + pH/Redox + 3 Schlauchpumpen | Eigene Steuerung statt Fertiganlage; Durchflussverriegelung zwingend
Entlüftung First | je VL/RL T-Stück + Kugelhahn + Autoentlüfter | Höchster Punkt sammelt Luft; Kugelhahn zum Tauschen
MAG | Bestand bleibt, Größe/Einstellung prüfen | Bei zusätzlichem Wasservolumen der neuen Leitungen ggf. größer nötig

Sheet: Quellen & Hinweise
Quelle / Link | Wofür verwendet | Stand / Hinweis
https://www.kwerk.de/rohrsysteme/pp-rct-rohrsysteme/pp-rct-rohre/rohre-mehrlagig/stabitec-ct/pp-rct-alu-druckrohr-stabitec-ct-20mpa-gruen/ | PP-RCT Stabi/Alu sauerstoffdicht nach DIN 4726; Rohr/Fitting-Quelle | Preis/Verfügbarkeit prüfen
https://www.rohrleitungssysteme.de/pp-r-rohrsysteme/index.php?zurueck=1 | PP-R/PP-RCT Rohrsysteme und Fittings | Alternative Quelle / Kategorie
https://www.plast24.de/kunststoffsysteme/pp-r-rct-rohrsysteme/werkzeuge/schweissgeraet/ | PP-RCT/PPR Schweißwerkzeuge | System-/Werkzeugbezug
https://chm-pumpen.de/Heizungspumpe-Auto-25-80-180/248 | Günstige 25-80 Heizungspumpe | Billigvariante
https://www.idealo.de/preisvergleich/OffersOfProduct/5142303_-alpha2-32-80-180mm-grundfos.html | Grundfos Alpha2 32-80 Preisvergleich | Premium-/Vergleichspumpe
https://www.idealo.de/preisvergleich/Liste/116030402/2-wege-motorkugelhahn-230v.html | 2-Wege Motorkugelhahn 230 V Preisvergleich | Billig-/Suchlink, technische Eignung prüfen
https://www.amazon.de/wege-motorkugelhahn-230v-elektrisch-kugelventil/dp/B07GCGFQ47 | 3-Wege Motorkugelhahn 230 V Beispiel | Billig-/Suchlink, technische Eignung prüfen
https://www.wiltec.de/wiltec-waermetauscher-50-platten-max.-285-kw-12-m3-h-2-50-l-je-durchgang-plattenwaermetauscher-aus-edelstahl-als-waermeuebertraeger/50683 | Plattenwärmetauscher groß / Brunnenkühlung | Edelstahl, Dimensionierung prüfen
https://www.schwimmbadbau24.de/Plattenwaermetauscher-PWT-50-kW-Edelstahl-geloetet | Pool-Plattenwärmetauscher 50 kW | Poolmaterial/Chlorid prüfen
https://www.gemke-shop.de/dosiertechnik/schwimmbad/elektroden/ | Acryl-Messzelle pH/Redox | Pooldosierung
https://www.idealo.de/preisvergleich/Liste/123483211/ph-elektrode-bnc-pool.html | pH-Elektrode BNC Preisvergleich | Pooldosierung
https://www.idealo.de/preisvergleich/Liste/123492102/redox-elektrode-pool.html | Redox-Elektrode Preisvergleich | Pooldosierung
https://www.antratek.de/industrial-ph-meter-sensor-modbus-rtu-rs485 | pH-Sensor mit Modbus/RS485 Beispiel | Messumformer/Steuerungsanbindung
https://www.idealo.de/preisvergleich/Liste/122043962/impfventil-1-2.html | Impfventile 1/2" Preisvergleich | Dosierstellen
https://www.amazon.de/s?k=peristaltische+dosierpumpe+12v | Schlauchpumpen Suchlink | Dosierpumpen
https://www.dincertco.de/din-certco/de/main-navigation/products-and-services/certification-of-products/raumheizung-und-k%C3%BChlung/rohrleitungen-aus-kunststo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 | Sauerstoffdichtheit nach DIN 4726 bei Kunststoff-Heizungsrohren | Technischer Hinweis
Summenhinweis | Die Summe in der Komponentenliste enthält nur grobe Richtwerte und Pauschalpositionen. Versand, Kleinteile, Gewindedichtungen, zusätzliche Bögen/Übergänge und Chemikalien sind nicht vollständig enthalten.
Empfohlene nächste Prüfung | Vor Einkauf: endgültige Rohrdimension, Pumpenförderhöhe, WT-Leistung, MAG-Größe, Frostschutzkonzept und elektrische Schutzmaßnahmen prüfen.
Grobe Summe Komponentenliste | 7308.00 €
