freezweb/de.freezweb.heizungssteuerung/tmp/watermeter-current/config.ini

[TakeImage]
;RawImagesLocation = undefined
;RawImagesRetention = 
WaitBeforeTakingPicture = 5
CamGainceiling = x8
CamQuality = 10
CamBrightness = 0
CamContrast = 0
CamSaturation = 0
CamSharpness = 2
CamAutoSharpness = false
CamSpecialEffect = no_effect
CamWbMode = auto
CamAwb = true
CamAwbGain = true
CamAec = true
CamAec2 = true
CamAeLevel = 2
CamAecValue = 600
CamAgc = true
CamAgcGain = 8
CamBpc = true
CamWpc = true
CamRawGma = true
CamLenc = true
CamHmirror = false
CamVflip = false
CamDcw = true
CamDenoise = 0
CamZoom = false
CamZoomOffsetX = 0
CamZoomOffsetY = 0
CamZoomSize = 0
LEDIntensity = 40
Demo = false

[Alignment]
InitialRotate = -6.0
SearchFieldX = 20
SearchFieldY = 20
AlignmentAlgo = Off

/config/ref0.jpg 248 37
/config/ref1.jpg 452 303
[Digits]
Model = /config/dig-cont_0900_s3_q.tflite
;CNNGoodThreshold = 
;ROIImagesLocation = undefined
;ROIImagesRetention = 
zaehlerstand.dig 249 100 27 45 0
zaehlerstand.dig2 290 100 24 40 0
zaehlerstand.dig3 330 100 24 40 0
zaehlerstand.dig4 363 100 28 40 0
zaehlerstand.dig5 400 100 32 45 0

[Analog]
Model = /config/ana-cont_1500_s2_q.tflite
;ROIImagesLocation = undefined
;ROIImagesRetention = 
zaehlerstand.ana1 421 184 62 62 false
zaehlerstand.ana2 388 253 64 64 false
zaehlerstand.ana3 316 283 64 64 false
zaehlerstand.ana4 211 243 64 64 false

[PostProcessing]
zaehlerstand.DecimalShift = 0
zaehlerstand.AnalogToDigitTransitionStart = 9.2
zaehlerstand.ChangeRateThreshold = 2
PreValueUse = true
;PreValueAgeStartup = 
zaehlerstand.AllowNegativeRates = false
zaehlerstand.MaxRateValue = 0.05
;zaehlerstand.MaxRateType = RateChange
zaehlerstand.ExtendedResolution = false
zaehlerstand.IgnoreLeadingNaN = false
ErrorMessage = false
zaehlerstand.CheckDigitIncreaseConsistency = false

;[MQTT]
Uri = mqtt://mqtt.esrv.center:1883
MainTopic = watermeter
ClientID = watermeter
user = vbnet
password = vbnet
RetainMessages = true
;DomoticzTopicIn = undefined
;zaehlerstand.DomoticzIDX = undefined
HomeassistantDiscovery = true
MeterType = water_m3
;CACert = undefined
;ClientCert = undefined
;ClientKey = undefined
;ValidateServerCert = true

;[InfluxDB]
;Uri = undefined
;Database = undefined
;user = undefined
;password = undefined
;zaehlerstand.Measurement = undefined
;zaehlerstand.Field = undefined

;[InfluxDBv2]
;Uri = undefined
;Bucket = undefined
;Org = undefined
;Token = undefined
;zaehlerstand.Measurement = undefined
;zaehlerstand.Field = undefined

;[Webhook]
;Uri = undefined
;ApiKey = undefined
;UploadImg = 0

;[GPIO]
;IO0 = input disabled false false  
;IO1 = input disabled false false  
;IO3 = input disabled false false  
;IO4 = input disabled false false  
;IO12 = input disabled false false  
;IO13 = input disabled false false  
LEDType = WS2812
LEDNumbers = 2
LEDColor = 50 50 50

[AutoTimer]
AutoStart = false
Interval = 5

;[DataLogging]
DataLog
