freezweb/de.freezweb.heizungssteuerung/homeassistant/packages/heizung_mqtt.yaml

mqtt:
  sensor:
    - name: "Tor Status"
      unique_id: heizung_tor_status
      state_topic: "heizung/tor/status"
      icon: mdi:gate

    - name: "Heizung Gesamt VL Soll"
      unique_id: heizung_gesamt_vl_soll
      state_topic: "heizung/gesamt/vl_soll/state"
      unit_of_measurement: "°C"
      device_class: temperature
      state_class: measurement

    - name: "Heizung Failsafe Grund"
      unique_id: heizung_failsafe_grund
      state_topic: "heizung/failsafe/grund"

    - name: "Heizung Routing"
      unique_id: heizung_routing_json
      state_topic: "heizung/routing/state"
      value_template: "{{ value_json.common_demands | join(', ') if value_json.common_demands is defined else value }}"
      json_attributes_topic: "heizung/routing/state"

    - name: "Heizung Waermebedarf"
      unique_id: heizung_gesamt_waermebedarf_kw
      state_topic: "heizung/gesamt/waermebedarf_kw/state"
      unit_of_measurement: "kW"
      device_class: power
      state_class: measurement

    - name: "WP Einzelleistung aktuell"
      unique_id: heizung_wp_einzelleistung_kw
      state_topic: "heizung/gesamt/wp_einzelleistung_kw/state"
      unit_of_measurement: "kW"
      device_class: power
      state_class: measurement

    - name: "WP Parallel Schwelle aktuell"
      unique_id: heizung_wp_parallel_schwelle_kw
      state_topic: "heizung/gesamt/wp_parallel_schwelle_kw/state"
      unit_of_measurement: "kW"
      device_class: power
      state_class: measurement

    - name: "Heizung VL Sammel"
      unique_id: heizung_temp_vl_sammel
      state_topic: "heizung/temp/vl_sammel/state"
      unit_of_measurement: "°C"
      device_class: temperature
      state_class: measurement

    - name: "Heizung RL Sammel"
      unique_id: heizung_temp_rl_sammel
      state_topic: "heizung/temp/rl_sammel/state"
      unit_of_measurement: "°C"
      device_class: temperature
      state_class: measurement

    - name: "Heizung Aussen"
      unique_id: heizung_temp_aussen
      state_topic: "heizung/temp/aussen/state"
      unit_of_measurement: "°C"
      device_class: temperature
      state_class: measurement

    - name: "Pool Wasser"
      unique_id: heizung_temp_pool_wasser
      state_topic: "heizung/temp/pool_wasser/state"
      unit_of_measurement: "°C"
      device_class: temperature
      state_class: measurement

    - name: "Pool WT VL"
      unique_id: heizung_temp_pool_wt_vl
      state_topic: "heizung/temp/pool_wt_vl/state"
      unit_of_measurement: "°C"
      device_class: temperature
      state_class: measurement

    - name: "Pool WT RL"
      unique_id: heizung_temp_pool_wt_rl
      state_topic: "heizung/temp/pool_wt_rl/state"
      unit_of_measurement: "°C"
      device_class: temperature
      state_class: measurement

    - name: "Nebengebaeude VL"
      unique_id: heizung_temp_vl_nebengeb
      state_topic: "heizung/temp/vl_nebengeb/state"
      unit_of_measurement: "°C"
      device_class: temperature
      state_class: measurement

    - name: "Nebengebaeude RL"
      unique_id: heizung_temp_rl_nebengeb
      state_topic: "heizung/temp/rl_nebengeb/state"
      unit_of_measurement: "°C"
      device_class: temperature
      state_class: measurement

    - name: "Brauchwasser Oben"
      unique_id: heizung_temp_bw_oben
      state_topic: "heizung/temp/bw_oben/state"
      unit_of_measurement: "°C"
      device_class: temperature
      state_class: measurement

    - name: "Brauchwasser Unten"
      unique_id: heizung_temp_bw_unten
      state_topic: "heizung/temp/bw_unten/state"
      unit_of_measurement: "°C"
      device_class: temperature
      state_class: measurement

    - name: "Brauchwasser Ladegrund"
      unique_id: heizung_brauchwasser_ladegrund
      state_topic: "heizung/brauchwasser/grund"

    - name: "Ausgang Brunnen FU Soll"
      unique_id: heizung_hauptsteuerung_ausgang_brunnen_fu_soll
      state_topic: "heizung/ao/brunnen_fu_soll/state"
      unit_of_measurement: "%"
      state_class: measurement

  binary_sensor:
    - name: "Heizung Gesamt Aktiv"
      unique_id: heizung_gesamt_active
      state_topic: "heizung/gesamt/active"
      payload_on: "1"
      payload_off: "0"

    - name: "Heizung Failsafe Aktiv"
      unique_id: heizung_failsafe_active
      state_topic: "heizung/failsafe/active"
      payload_on: "1"
      payload_off: "0"
      device_class: problem

    - name: "Brauchwasser Ladung Aktiv"
      unique_id: heizung_brauchwasser_ladung_aktiv
      state_topic: "heizung/brauchwasser/ladung_aktiv"
      payload_on: "1"
      payload_off: "0"

    - name: "Tor Fluegel Links Zu"
      unique_id: heizung_tor_fluegel_links_zu
      state_topic: "heizung/di/tor_fluegel_links_zu/state"
      payload_on: "1"
      payload_off: "0"

    - name: "Tor Fluegel Rechts Zu"
      unique_id: heizung_tor_fluegel_rechts_zu
      state_topic: "heizung/di/tor_fluegel_rechts_zu/state"
      payload_on: "1"
      payload_off: "0"

    - name: "Tor Lichtschranke"
      unique_id: heizung_tor_lichtschranke
      state_topic: "heizung/di/tor_lichtschranke/state"
      payload_on: "0"
      payload_off: "1"
      device_class: safety

    - name: "WP1 Stoerung"
      unique_id: heizung_wp1_stoerung
      state_topic: "heizung/di/wp1_stoerung/state"
      payload_on: "1"
      payload_off: "0"
      device_class: problem

    - name: "WP2 Stoerung"
      unique_id: heizung_wp2_stoerung
      state_topic: "heizung/di/wp2_stoerung/state"
      payload_on: "1"
      payload_off: "0"
      device_class: problem

    - name: "Ausgang Brunnen Pumpe Freigabe"
      unique_id: heizung_hauptsteuerung_ausgang_brunnen_pumpe_freigabe
      state_topic: "heizung/do/brunnen_pumpe_freigabe/state"
      payload_on: "1"
      payload_off: "0"

    - name: "Hand Aktiv Brunnen Pumpe Freigabe"
      unique_id: heizung_hauptsteuerung_hand_aktiv_brunnen_pumpe_freigabe
      state_topic: "heizung/brunnen_pumpe_freigabe/hand/mode/state"
      payload_on: "1"
      payload_off: "0"

    - name: "Hand Aktiv Brunnen FU Soll"
      unique_id: heizung_hauptsteuerung_hand_aktiv_brunnen_fu_soll
      state_topic: "heizung/brunnen_fu_soll/hand/mode/state"
      payload_on: "1"
      payload_off: "0"

  switch:
    - name: "Freigabe Oelbrenner"
      unique_id: heizung_freigabe_oelbrenner
      state_topic: "heizung/freigabe/quellen/oelbrenner/state"
      command_topic: "heizung/freigabe/quellen/oelbrenner/set"
      payload_on: "1"
      payload_off: "0"
      state_on: "1"
      state_off: "0"

    - name: "Freigabe WP1"
      unique_id: heizung_freigabe_wp1
      state_topic: "heizung/freigabe/quellen/wp1/state"
      command_topic: "heizung/freigabe/quellen/wp1/set"
      payload_on: "1"
      payload_off: "0"
      state_on: "1"
      state_off: "0"

    - name: "Freigabe WP2"
      unique_id: heizung_freigabe_wp2
      state_topic: "heizung/freigabe/quellen/wp2/state"
      command_topic: "heizung/freigabe/quellen/wp2/set"
      payload_on: "1"
      payload_off: "0"
      state_on: "1"
      state_off: "0"

    - name: "Freigabe BWWP"
      unique_id: heizung_freigabe_bwwp
      state_topic: "heizung/freigabe/quellen/bwwp/state"
      command_topic: "heizung/freigabe/quellen/bwwp/set"
      payload_on: "1"
      payload_off: "0"
      state_on: "1"
      state_off: "0"

    - name: "Freigabe FBH EG"
      unique_id: heizung_freigabe_fbh_eg
      state_topic: "heizung/freigabe/senken/fbh_eg/state"
      command_topic: "heizung/freigabe/senken/fbh_eg/set"
      payload_on: "1"
      payload_off: "0"
      state_on: "1"
      state_off: "0"

    - name: "Freigabe Klima OG"
      unique_id: heizung_freigabe_klima_og
      state_topic: "heizung/freigabe/senken/klima_og/state"
      command_topic: "heizung/freigabe/senken/klima_og/set"
      payload_on: "1"
      payload_off: "0"
      state_on: "1"
      state_off: "0"

    - name: "Freigabe Nebengebaeude"
      unique_id: heizung_freigabe_nebengeb
      state_topic: "heizung/freigabe/senken/nebengeb/state"
      command_topic: "heizung/freigabe/senken/nebengeb/set"
      payload_on: "1"
      payload_off: "0"
      state_on: "1"
      state_off: "0"

    - name: "Freigabe HK Backup"
      unique_id: heizung_freigabe_hk_backup
      state_topic: "heizung/freigabe/senken/hk_backup/state"
      command_topic: "heizung/freigabe/senken/hk_backup/set"
      payload_on: "1"
      payload_off: "0"
      state_on: "1"
      state_off: "0"

    - name: "Freigabe Pool"
      unique_id: heizung_freigabe_pool
      state_topic: "heizung/freigabe/senken/pool/state"
      command_topic: "heizung/freigabe/senken/pool/set"
      payload_on: "1"
      payload_off: "0"
      state_on: "1"
      state_off: "0"

    - name: "Freigabe Brauchwasser"
      unique_id: heizung_freigabe_brauchwasser
      state_topic: "heizung/freigabe/senken/brauchwasser/state"
      command_topic: "heizung/freigabe/senken/brauchwasser/set"
      payload_on: "1"
      payload_off: "0"
      state_on: "1"
      state_off: "0"

    - name: "PV Ueberschuss"
      unique_id: heizung_pv_ueberschuss
      state_topic: "heizung/pv/ueberschuss/state"
      command_topic: "heizung/pv/ueberschuss/set"
      payload_on: "1"
      payload_off: "0"
      state_on: "1"
      state_off: "0"

    - name: "PV Mangel"
      unique_id: heizung_pv_mangel
      state_topic: "heizung/pv/mangel/state"
      command_topic: "heizung/pv/mangel/set"
      payload_on: "1"
      payload_off: "0"
      state_on: "1"
      state_off: "0"

    - name: "Handwert Brunnen Pumpe Freigabe"
      unique_id: heizung_hauptsteuerung_handwert_brunnen_pumpe_freigabe
      state_topic: "heizung/brunnen_pumpe_freigabe/hand/value/state"
      command_topic: "heizung/brunnen_pumpe_freigabe/hand/set"
      payload_on: "1"
      payload_off: "0"
      state_on: "1"
      state_off: "0"

  number:
    - name: "Handwert Brunnen FU Soll"
      unique_id: heizung_hauptsteuerung_handwert_brunnen_fu_soll
      state_topic: "heizung/brunnen_fu_soll/hand/value/state"
      command_topic: "heizung/brunnen_fu_soll/hand/set"
      min: 0
      max: 100
      step: 0.1
      unit_of_measurement: "%"
      mode: box

  button:
    - name: "Auto Brunnen Pumpe Freigabe"
      unique_id: heizung_hauptsteuerung_auto_brunnen_pumpe_freigabe
      command_topic: "heizung/brunnen_pumpe_freigabe/hand/auto"
      payload_press: "1"

    - name: "Auto Brunnen FU Soll"
      unique_id: heizung_hauptsteuerung_auto_brunnen_fu_soll
      command_topic: "heizung/brunnen_fu_soll/hand/auto"
      payload_press: "1"

    - name: "Tor Oeffnen Ganz"
      unique_id: heizung_tor_oeffnen_ganz
      command_topic: "heizung/tor/oeffnen_ganz/cmd"
      payload_press: "1"

    - name: "Tor Schliessen"
      unique_id: heizung_tor_schliessen
      command_topic: "heizung/tor/schliessen/cmd"
      payload_press: "1"

input_boolean:
  heizung_anf_fbh_eg:
    name: "Anforderung FBH EG"
  heizung_anf_klima_og:
    name: "Anforderung Klima OG"
  heizung_anf_nebengeb:
    name: "Anforderung Nebengebaeude"
  heizung_anf_pool:
    name: "Anforderung Pool"
  heizung_anf_bwwp:
    name: "Anforderung BWWP"
  heizung_r421b16_modbus_alarm_gesendet:
    name: "Heizung R421B16 Modbus Alarm Gesendet"
    icon: mdi:bell-check

input_number:
  heizung_vl_fbh_eg:
    name: "VL Soll FBH EG"
    min: 20
    max: 55
    step: 0.5
    unit_of_measurement: "°C"
  heizung_vl_hk_backup:
    name: "VL Soll HK Backup"
    min: 20
    max: 55
    step: 0.5
    unit_of_measurement: "C"
  heizung_vl_klima_og:
    name: "VL Soll Klima OG"
    min: 7
    max: 55
    step: 0.5
    unit_of_measurement: "°C"
  heizung_vl_nebengeb:
    name: "VL Soll Nebengebaeude"
    min: 20
    max: 55
    step: 0.5
    unit_of_measurement: "°C"
  heizung_vl_pool:
    name: "VL Soll Pool"
    min: 20
    max: 45
    step: 0.5
    unit_of_measurement: "°C"
  heizung_vl_bwwp:
    name: "VL Soll BWWP"
    min: 40
    max: 65
    step: 0.5
    unit_of_measurement: "°C"

automation:
  - alias: "Heizung Gebaeudeanforderungen an RevPi senden"
    id: heizung_sync_gebaeudeanforderungen_revpi
    description: "Sendet die RevPi-MQTT-Anforderungen mit Solltemperatur und berechnetem Waermebedarf aus HA."
    mode: restart
    trigger:
      - platform: homeassistant
        event: start
      - platform: time_pattern
        minutes: "/5"
      - platform: state
        entity_id:
          - sensor.heizanforderung_eg_prozent
          - sensor.heizanforderung_og_prozent
          - input_number.heizung_vl_fbh_eg
          - input_number.heizung_vl_hk_backup
          - number.heizung_kuche_ventilstellung
          - number.wohnzimmer_1_ventilstellung
          - number.wohnzimmer_2_ventilstellung
          - number.wohnzimmer_3_ventilstellung
          - number.heizung_eg_bad_ventilstellung
          - number.heizung_flur_eg_ventilstellung
          - sensor.shellyblutrv_f844772c4513_valve_position
          - sensor.shellyblutrv_f8447705cec4_valve_position_2
          - sensor.shellyblutrv_f844772090fd_valve_position
          - sensor.shellyblutrv_f844772ca365_valve_position
          - sensor.shellyblutrv_f844772c36fd_valve_position
    action:
      - service: mqtt.publish
        data:
          topic: "heizung/anforderung/fbh_eg/set"
          retain: true
          payload: >-
            {% set fallback = states('sensor.heizanforderung_eg_prozent') | float(0) %}
            {% set rooms = [
              ('number.heizung_kuche_ventilstellung', 1.20),
              ('number.wohnzimmer_1_ventilstellung', 1.25),
              ('number.wohnzimmer_2_ventilstellung', 1.25),
              ('number.wohnzimmer_3_ventilstellung', 1.25),
              ('number.heizung_eg_bad_ventilstellung', 0.59),
              ('number.heizung_flur_eg_ventilstellung', 1.33)
            ] %}
            {% set ns = namespace(kw=0) %}
            {% for entity, kw in rooms %}
              {% set raw = states(entity) %}
              {% set pct = fallback if raw in ['unknown', 'unavailable', 'none', ''] else raw | float(0) %}
              {% set ns.kw = ns.kw + (pct / 100 * kw) %}
            {% endfor %}
            {{ {
              'aktiv': ns.kw > 0.05,
              'vl_soll': states('input_number.heizung_vl_fbh_eg') | float(30),
              'leistung_kw': ns.kw | round(2),
              'quelle': 'ha_leistungsbedarf'
            } | to_json }}
      - service: mqtt.publish
        data:
          topic: "heizung/anforderung/hk_backup/set"
          retain: true
          payload: >-
            {% set fallback = states('sensor.heizanforderung_og_prozent') | float(0) %}
            {% set rooms = [
              ('sensor.shellyblutrv_f844772c4513_valve_position', 2.05),
              ('sensor.shellyblutrv_f8447705cec4_valve_position_2', 1.15),
              ('sensor.shellyblutrv_f844772090fd_valve_position', 1.60),
              ('sensor.shellyblutrv_f844772ca365_valve_position', 0.82),
              ('sensor.shellyblutrv_f844772c36fd_valve_position', 0.82)
            ] %}
            {% set ns = namespace(kw=0) %}
            {% for entity, kw in rooms %}
              {% set raw = states(entity) %}
              {% set pct = fallback if raw in ['unknown', 'unavailable', 'none', ''] else raw | float(0) %}
              {% set ns.kw = ns.kw + (pct / 100 * kw) %}
            {% endfor %}
            {{ {
              'aktiv': ns.kw > 0.05,
              'vl_soll': states('input_number.heizung_vl_hk_backup') | float(40),
              'leistung_kw': ns.kw | round(2),
              'quelle': 'ha_leistungsbedarf'
            } | to_json }}

  - alias: "Heizung HA Heartbeat"
    id: heizung_ha_heartbeat
    trigger:
      - platform: time_pattern
        seconds: "/60"
    action:
      - service: mqtt.publish
        data:
          topic: "heizung/ha/heartbeat"
          payload_template: "{{ now().timestamp() | int }}"

  - alias: "Heizung Oelbrenner Sicherheitsmeldungen Telegram"
    id: heizung_oelbrenner_stoerung_telegram
    mode: queued
    max: 10
    trigger:
      - platform: state
        entity_id: binary_sensor.heizung_hauptsteuerung_oelbrenner_stoermeldung
        from: "off"
        to: "on"
        for: "00:00:02"
      - platform: state
        entity_id: binary_sensor.heizung_hauptsteuerung_oelbrenner_stoermeldung
        from: "on"
        to: "off"
        for: "00:00:02"
      - platform: state
        entity_id: binary_sensor.heizung_hauptsteuerung_oelbrenner_wasserdruck_stoerung
        from: "off"
        to: "on"
        for: "00:00:02"
      - platform: state
        entity_id: binary_sensor.heizung_hauptsteuerung_oelbrenner_wasserdruck_stoerung
        from: "on"
        to: "off"
        for: "00:00:02"
      - platform: state
        entity_id: binary_sensor.heizung_hauptsteuerung_oelbrenner_stb_stoerung
        from: "off"
        to: "on"
        for: "00:00:02"
      - platform: state
        entity_id: binary_sensor.heizung_hauptsteuerung_oelbrenner_stb_stoerung
        from: "on"
        to: "off"
        for: "00:00:02"
    action:
      - service: telegram_bot.send_message
        continue_on_error: true
        data:
          parse_mode: plain_text
          chat_id:
            - "-4649956506"
          message: >-
            {% set meldung = trigger.to_state.attributes.friendly_name | default(trigger.entity_id) %}
            {% if trigger.to_state.state == 'on' %}
            Heizung: {{ meldung }} erkannt.
            {% else %}
            Heizung: {{ meldung }} wieder OK.
            {% endif %}
            Betriebsmeldung: {{ states('binary_sensor.heizung_hauptsteuerung_oelbrenner_betriebsmeldung') }}.
            Zeit: {{ now().strftime('%Y-%m-%d %H:%M:%S') }}.
      - service: persistent_notification.create
        data:
          title: >-
            {% if trigger.to_state.state == 'on' %}
            Heizung: Oelbrenner Stoerung
            {% else %}
            Heizung: Oelbrenner wieder OK
            {% endif %}
          message: >-
            {{ trigger.to_state.attributes.friendly_name | default(trigger.entity_id) }} ist {{ 'aktiv' if trigger.to_state.state == 'on' else 'wieder OK' }}.

  - alias: "Heizung R421B16 Modbus Telegram"
    id: heizung_r421b16_modbus_telegram
    description: "Sendet die OK-Meldung nur, wenn vorher wirklich ein Stoeralarm verschickt wurde."
    mode: queued
    max: 5
    trigger:
      - platform: state
        id: down
        entity_id: binary_sensor.heizung_hauptsteuerung_r421b16_modbus_stoerung
        from: "off"
        to: "on"
        for: "00:00:10"
      - platform: state
        id: up
        entity_id: binary_sensor.heizung_hauptsteuerung_r421b16_modbus_stoerung
        from: "on"
        to: "off"
        for: "00:00:10"
    action:
      - choose:
          - conditions:
              - condition: template
                value_template: "{{ trigger.id == 'down' }}"
            sequence:
              - service: telegram_bot.send_message
                continue_on_error: true
                data:
                  parse_mode: plain_text
                  chat_id:
                    - "-4649956506"
                  message: >-
                    Heizung: R421B16 Keller-Relaismodul ist nicht erreichbar.
                    Fehler: {{ states('sensor.heizung_hauptsteuerung_r421b16_modbus_fehler') }}.
                    Zeit: {{ now().strftime('%Y-%m-%d %H:%M:%S') }}.
              - service: persistent_notification.create
                data:
                  title: "Heizung: R421B16 Modbus Stoerung"
                  message: >-
                    Das Keller-Relaismodul 10.1.100.169 antwortet nicht auf den zyklischen Modbus-Statuspoll.
                    Fehler: {{ states('sensor.heizung_hauptsteuerung_r421b16_modbus_fehler') }}.
              - service: input_boolean.turn_on
                target:
                  entity_id: input_boolean.heizung_r421b16_modbus_alarm_gesendet
          - conditions:
              - condition: template
                value_template: "{{ trigger.id == 'up' }}"
              - condition: state
                entity_id: input_boolean.heizung_r421b16_modbus_alarm_gesendet
                state: "on"
            sequence:
              - service: telegram_bot.send_message
                continue_on_error: true
                data:
                  parse_mode: plain_text
                  chat_id:
                    - "-4649956506"
                  message: >-
                    Heizung: R421B16 Keller-Relaismodul ist wieder erreichbar.
                    Zeit: {{ now().strftime('%Y-%m-%d %H:%M:%S') }}.
              - service: persistent_notification.create
                data:
                  title: "Heizung: R421B16 Modbus wieder OK"
                  message: "Das Keller-Relaismodul antwortet wieder."
              - service: input_boolean.turn_off
                target:
                  entity_id: input_boolean.heizung_r421b16_modbus_alarm_gesendet
